Jana-Marie/Otter-Iron/images/1.jpg

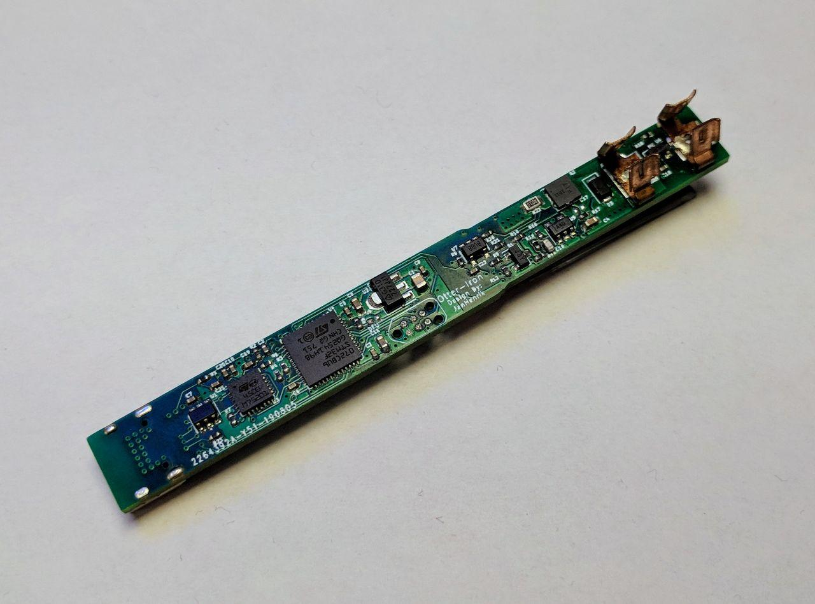
images/1.jpg
