Jana-Marie/Otter-Iron/images/2.jpg

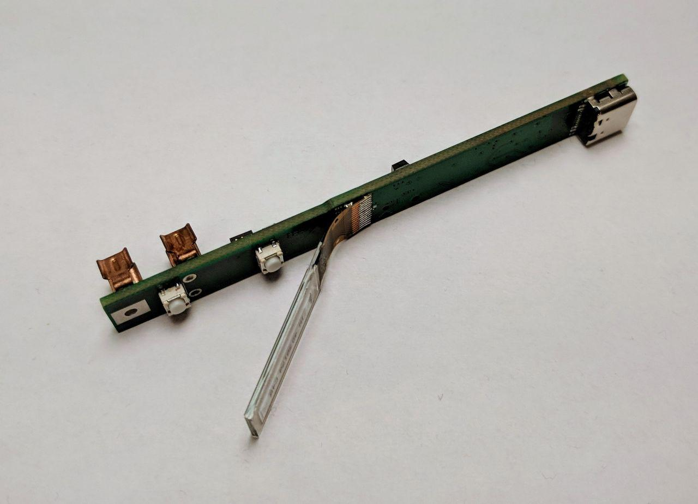
images/2.jpg
